verdanatesman/Elektrikli-Arac-Batarya-Yonetim-Sistemi-Tasarimi-ve-Uretimi/Proje Yapimi Gorseller/IMG-20230211-WA0025.jpg

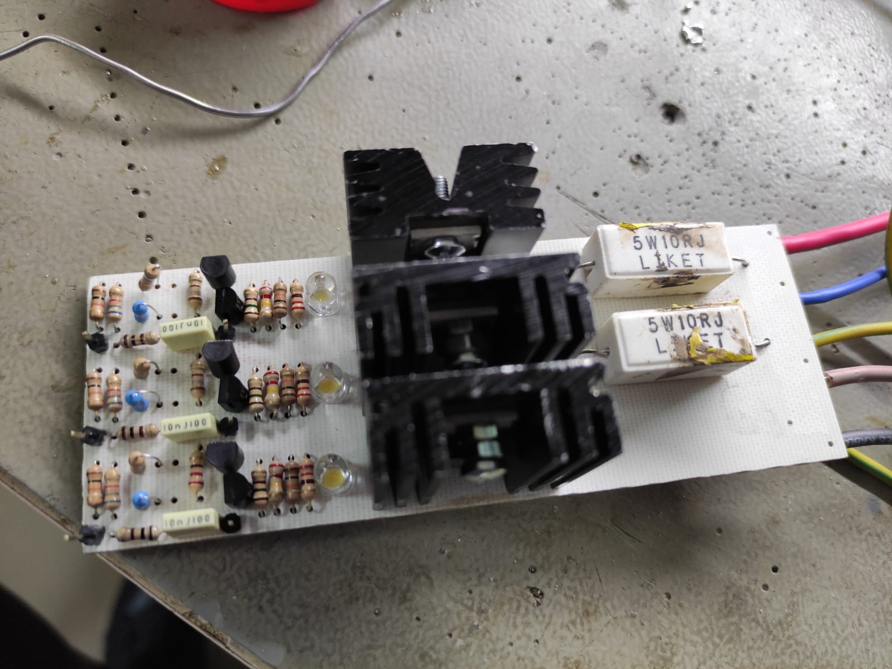
Proje Yapimi Gorseller/IMG-20230211-WA0025.jpg
