verdanatesman/Elektrikli-Arac-Batarya-Yonetim-Sistemi-Tasarimi-ve-Uretimi/Proje Yapimi Gorseller/IMG-20230211-WA0036.jpg

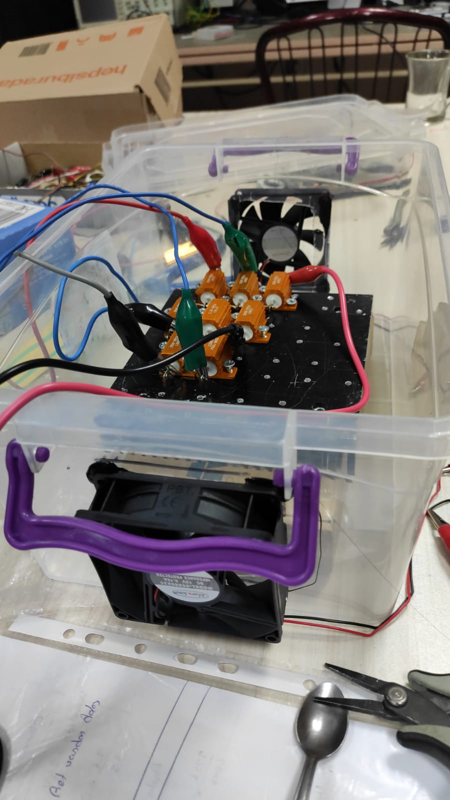
Proje Yapimi Gorseller/IMG-20230211-WA0036.jpg
