verdanatesman/Elektrikli-Arac-Batarya-Yonetim-Sistemi-Tasarimi-ve-Uretimi/Tasarim Gorselleri/batarya sıcaklık sensör noktaları.JPG

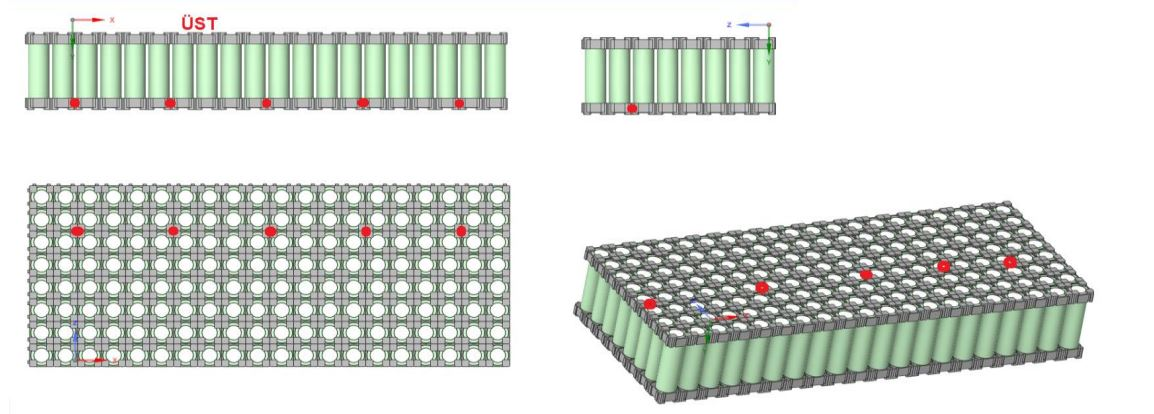
Tasarim Gorselleri/batarya sıcaklık sensör noktaları.JPG
