verdanatesman/Elektrikli-Arac-Batarya-Yonetim-Sistemi-Tasarimi-ve-Uretimi/Tasarim Gorselleri/kontrol algoritması.JPG

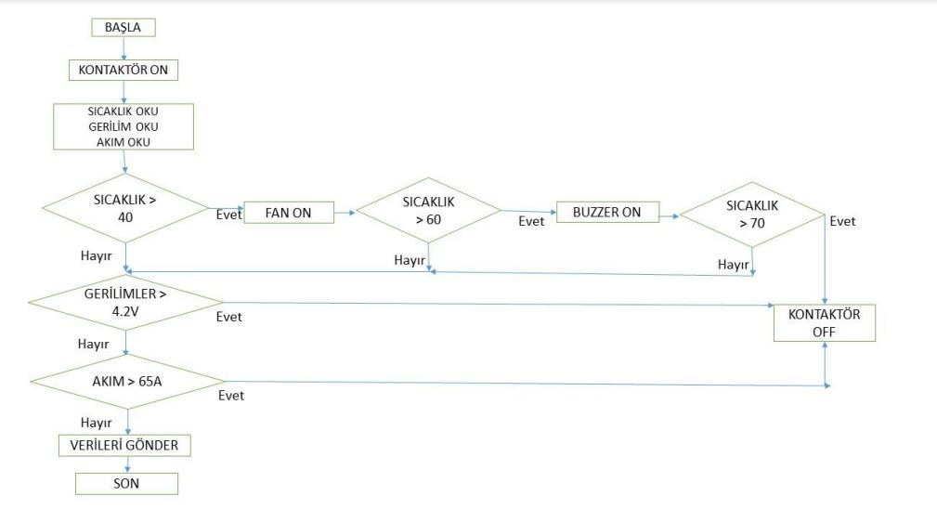
Tasarim Gorselleri/kontrol algoritması.JPG
