verdanatesman/Elektrikli-Arac-Batarya-Yonetim-Sistemi-Tasarimi-ve-Uretimi/Tasarim Gorselleri/paket tasarımı.JPG

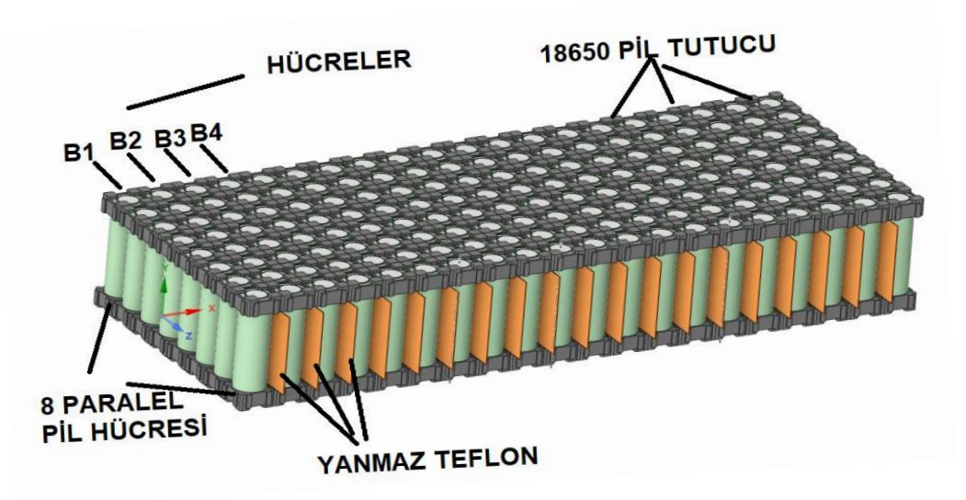
Tasarim Gorselleri/paket tasarımı.JPG
