verdanatesman/Elektrikli-Arac-Batarya-Yonetim-Sistemi-Tasarimi-ve-Uretimi/Tasarim Gorselleri/sıcaklık algoritması.JPG

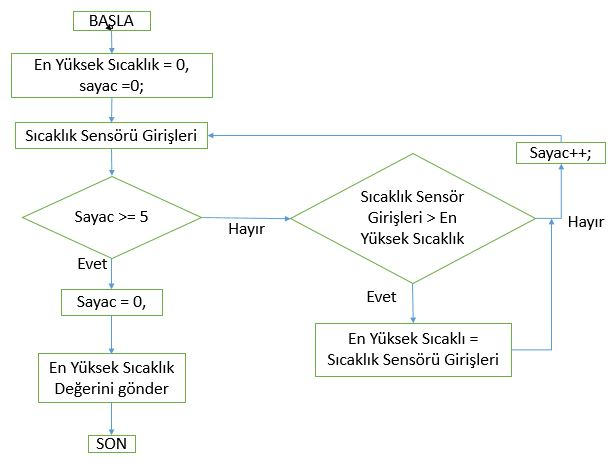
Tasarim Gorselleri/sıcaklık algoritması.JPG
