verdanatesman/Elektrikli-Arac-Batarya-Yonetim-Sistemi-Tasarimi-ve-Uretimi/Tasarim Gorselleri/TL431.JPG

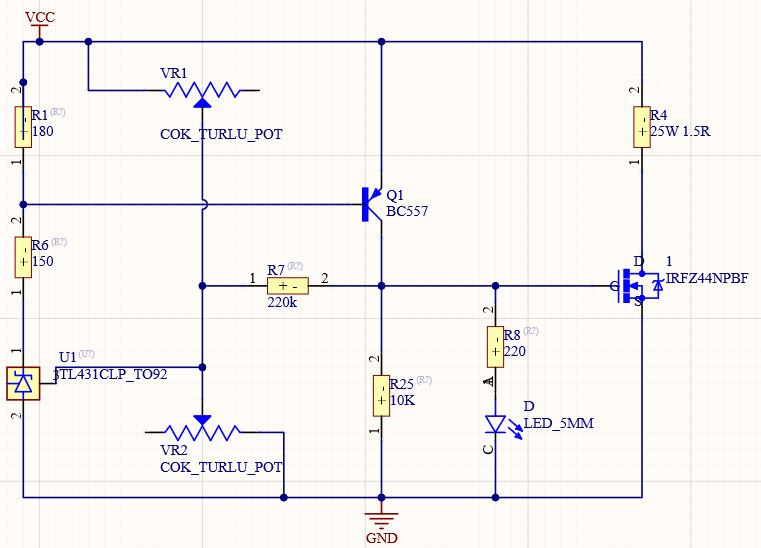
Tasarim Gorselleri/TL431.JPG
