verdanatesman/Elektrikli-Arac-Batarya-Yonetim-Sistemi-Tasarimi-ve-Uretimi/Tasarim Gorselleri/3 devre pcb test.JPG

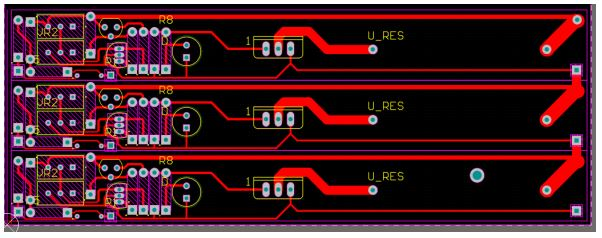
Tasarim Gorselleri/3 devre pcb test.JPG
